Guimli/Vectrex-Pad-miniNeoGeo/Vectrex Pad miniNeoGeo.kicad_sch

## KiCad design Vectrex Pad miniNeoGeo.kicad_sch (2022-07-23)

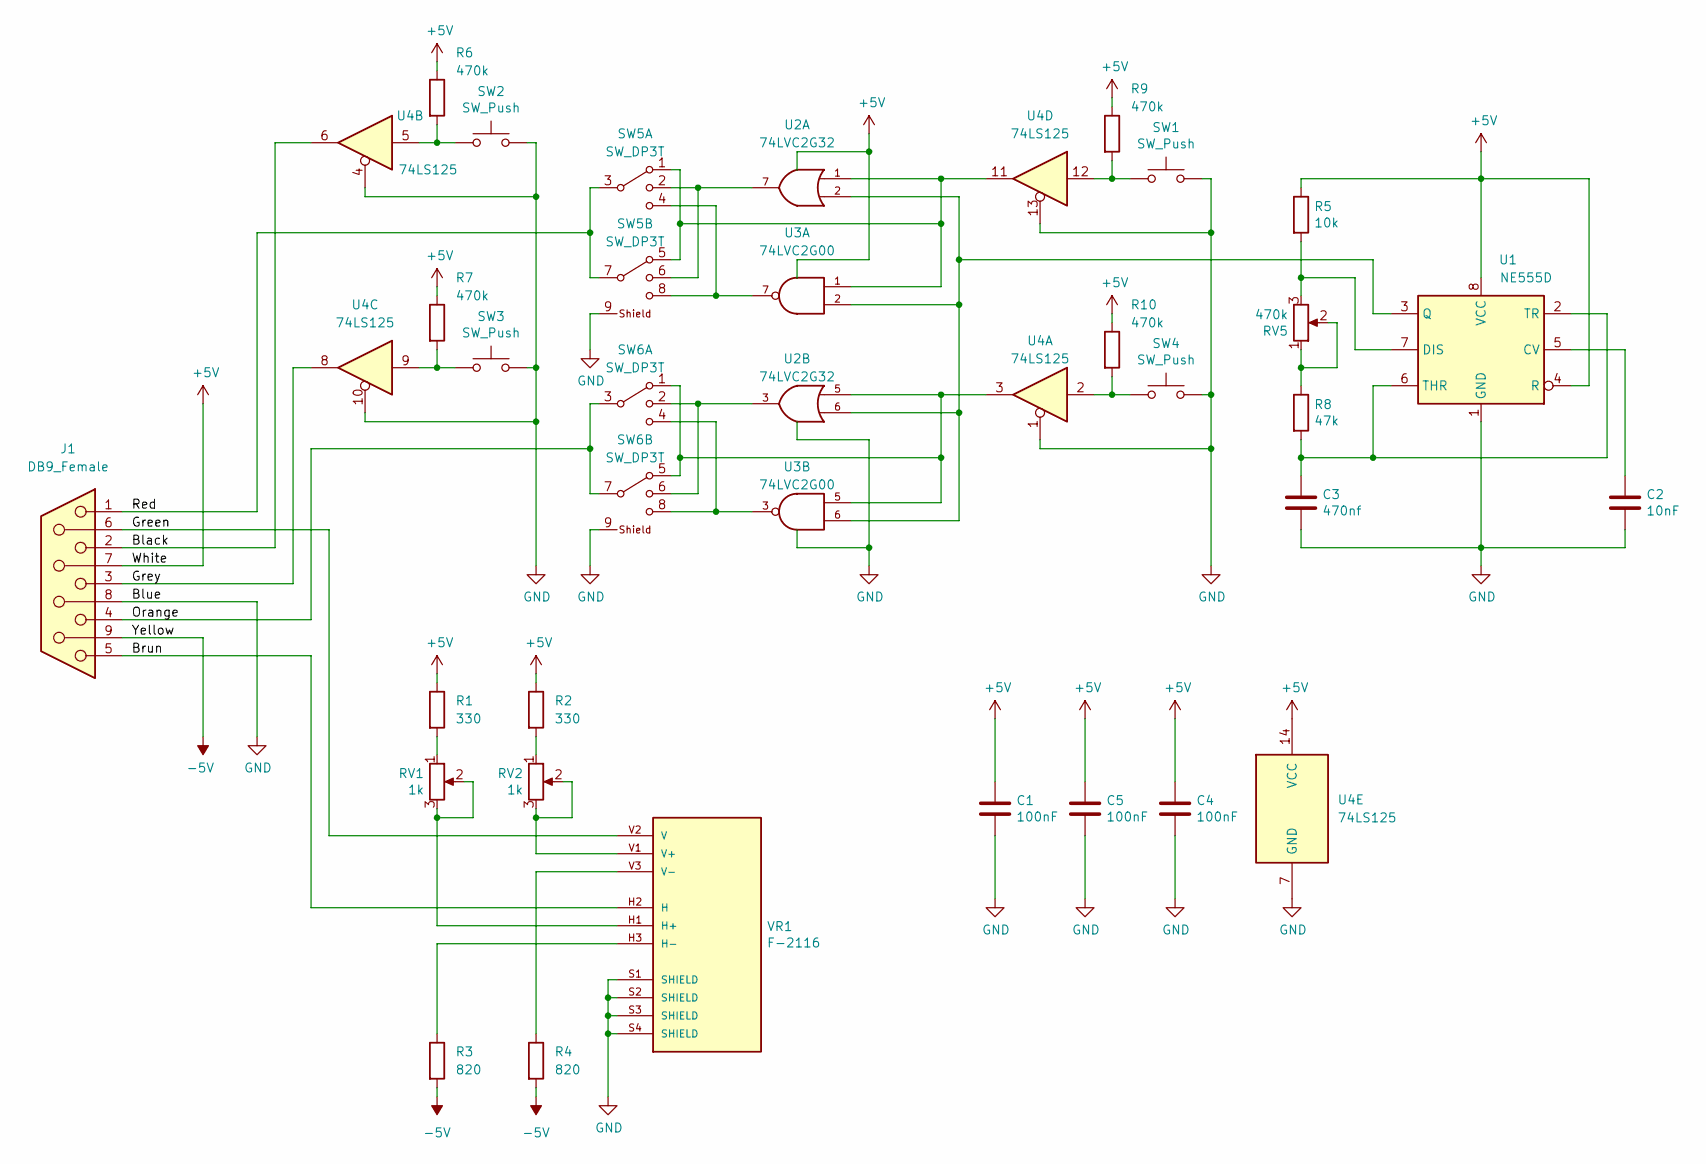
[picture p10: schematic Vectrex Pad miniNeoGeo.kicad_sch]

Parts:
C1, C4, C5: 100nF; C_0805_2012Metric
C2: 10nF; C_0805_2012Metric
C3: 470nf; C_0805_2012Metric
J1: DB9_Female; DB9
R1, R2: 330; R_0805_2012Metric
R3, R4: 820; R_0805_2012Metric
R5: 10k; R_0805_2012Metric
R6, R7, R9, R10: 470k; R_0805_2012Metric
R8: 47k; R_0805_2012Metric
RV1, RV2: 1k; Potentiometer_ACP_CA9-V10_Vertical_Hole
RV5: 470k; Potentiometer_ACP_CA9-V10_Vertical_Hole
SW1, SW2, SW3, SW4: SW_Push; Silicon Button 5mm Medium
SW5, SW6: SW_DP3T; OS203011MS1QP1
U1: NE555D; TSSOP-8_4.4x3mm_P0.65mm
U2: 74LVC2G32; SSOP-8_2.95x2.8mm_P0.65mm
U3: 74LVC2G00; SSOP-8_2.95x2.8mm_P0.65mm
U4: 74LS125; TSSOP-14_4.4x5mm_P0.65mm
VR1: F-2116; PARTREV N/A

Connections:
+5V: C1.1, C4.1, C5.1, J1.7, R1.1, R2.1, R5.1, R6.1, R7.1, R9.1, R10.1, U1.4 (R), U1.8 (VCC), U2.8 (VCC), U3.8 (VCC), U4.14 (VCC)
-5V: J1.9, R3.2, R4.2
Black: J1.2, U4.6
Brun: J1.5, VR1.H2 (H)
GND: C1.2, C2.2, C3.2, C4.2, C5.2, J1.8, SW1.2, SW2.2, SW3.2, SW4.2, SW5.9 (Shield), SW6.9 (Shield), U1.1 (GND), U2.4 (GND), U3.4 (GND), U4.1, U4.4, U4.7 (GND), U4.10, U4.13, VR1.S1 (SHIELD), VR1.S2 (SHIELD), VR1.S3 (SHIELD), VR1.S4 (SHIELD)
Green: J1.6, VR1.V2 (V)
Grey: J1.3, U4.8
unnamed: C2.1, U1.5 (CV)
unnamed: C3.1, R8.2, U1.2 (TR), U1.6 (THR)
unnamed: R1.2, RV1.1
unnamed: R2.2, RV2.1
unnamed: R3.1, VR1.H3 (H-)
unnamed: R4.1, VR1.V3 (V-)
unnamed: R5.2, RV5.3, U1.7 (DIS)
unnamed: R6.2, SW2.1, U4.5
unnamed: R7.2, SW3.1, U4.9
unnamed: R8.1, RV5.1, RV5.2
unnamed: R9.2, SW1.1, U4.12
unnamed: R10.2, SW4.1, U4.2
unnamed: RV1.2, RV1.3, VR1.H1 (H+)
unnamed: RV2.2, RV2.3, VR1.V1 (V+)
unnamed: SW5.1, SW5.5, U2.1, U3.1, U4.11
unnamed: SW5.2, SW5.6, U2.7
unnamed: SW5.4, SW5.8, U3.7
unnamed: SW6.1, SW6.5, U2.5, U3.5, U4.3
unnamed: SW6.2, SW6.6, U2.3
unnamed: SW6.4, SW6.8, U3.3
unnamed: U1.3 (Q), U2.2, U2.6, U3.2, U3.6
Orange: J1.4, SW6.3, SW6.7
Red: J1.1, SW5.3, SW5.7
